NerdyProjects/HouseBusNode/sw/modules/modules.h

/*
 * modules.h
 *
 *  Created on: 20.11.2018
 *      Author: matthias
 */

#ifndef MODULES_MODULES_H_
#define MODULES_MODULES_H_
#include "time_data.h"
#include "brightness_data.h"
#include "temperature_receiver.h"
#include "obis.h"
#include "boiler.h"


#endif /* MODULES_MODULES_H_ */
