NerdyProjects/HouseBusNode/sw/modules/melodies.h

/*
 * melodies.h
 *
 *  Created on: 01.12.2018
 *      Author: matthias
 */

#ifndef MODULES_MELODIES_H_
#define MODULES_MELODIES_H_

#include "stdint.h"

typedef struct
{
  uint8_t note;
  uint8_t duration;
} note;

typedef note* melody;

void melody_play(uint8_t melody, uint8_t volume);
void melody_tick(void);

#endif /* MODULES_MELODIES_H_ */
