NerdyProjects/HouseBusNode/sw/bootloader.h

/*
 * bootloader.h
 *
 *  Created on: 27.01.2018
 *      Author: matthias
 */

#ifndef BOOTLOADER_H_
#define BOOTLOADER_H_

void bootloader_command_executed(void);
void bootloader_loop(void);

#endif /* BOOTLOADER_H_ */
